dlip/koumori/kicad/footprints/layer3.png

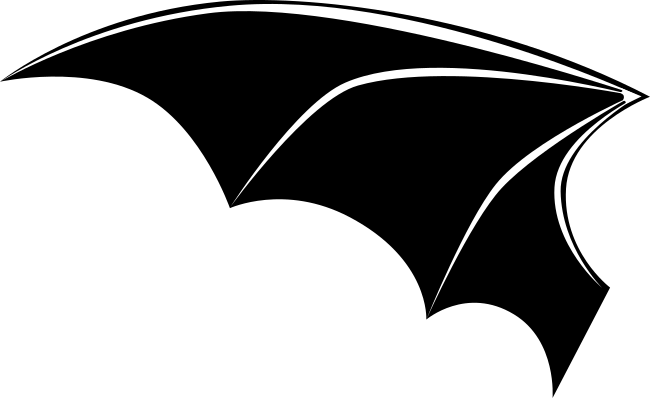
kicad/footprints/layer3.png
