dlip/koumori/kicad/footprints/text275.png

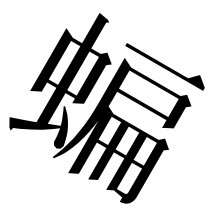
kicad/footprints/text275.png
